tomarc3/mySensors-EthRs485Gateway-Hardware/img/IMG_5391.jpg

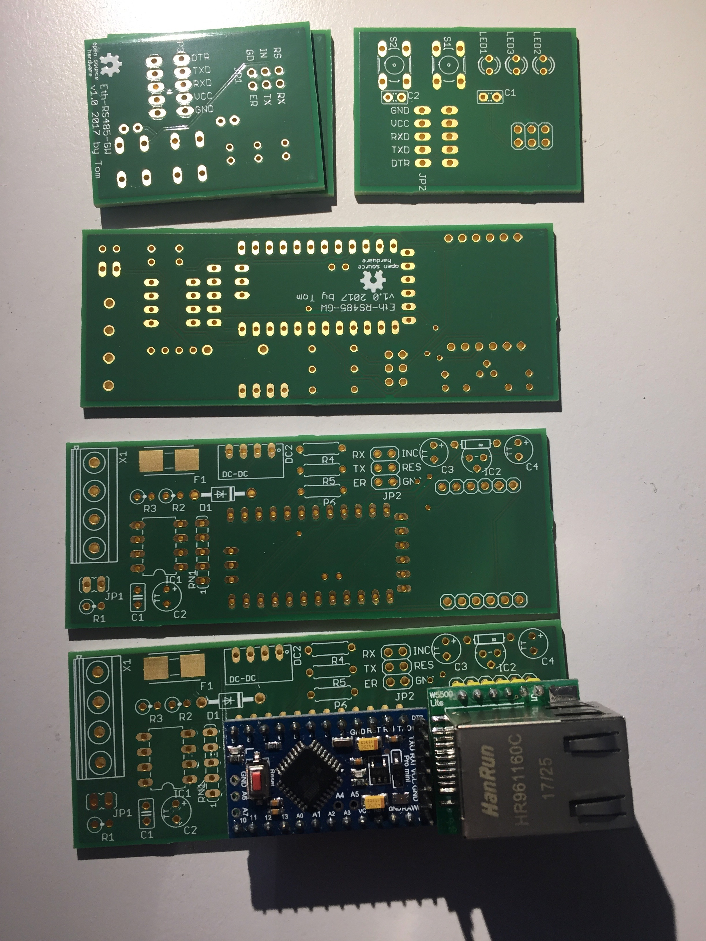
img/IMG_5391.jpg
